nkeeline/KeeCap-Open-Motion-Capture-Suit/Build Procedures/IMG_2735.JPG

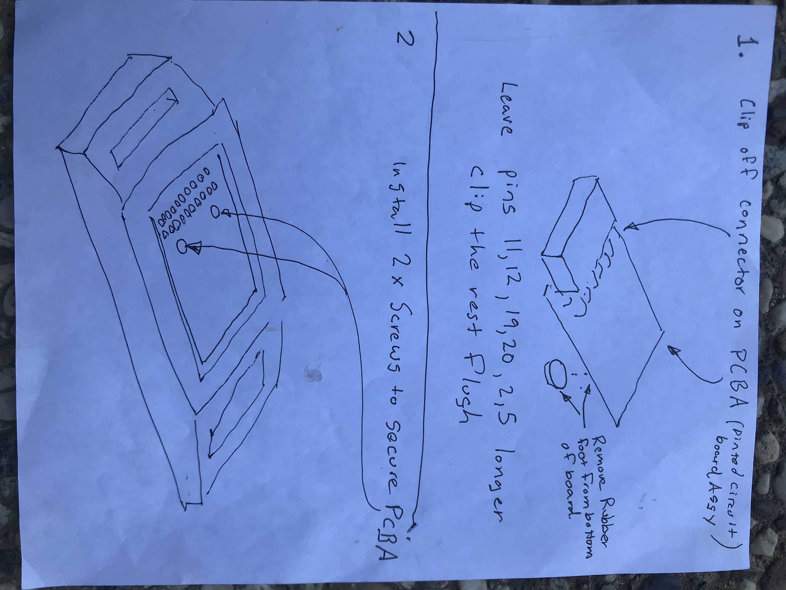
Build Procedures/IMG_2735.JPG
