nkeeline/KeeCap-Open-Motion-Capture-Suit/Build Procedures/IMG_2736.JPG

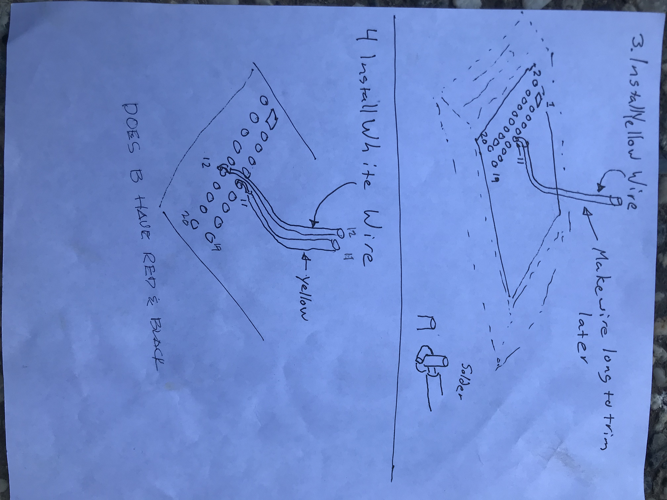
Build Procedures/IMG_2736.JPG
