nkeeline/KeeCap-Open-Motion-Capture-Suit/Build Procedures/IMG_2737.JPG

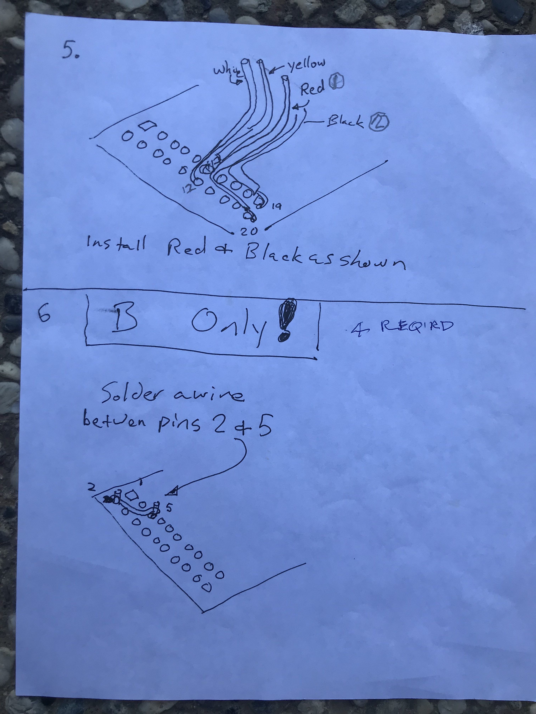
Build Procedures/IMG_2737.JPG
