nkeeline/KeeCap-Open-Motion-Capture-Suit/Build Procedures/IMG_2738.JPG

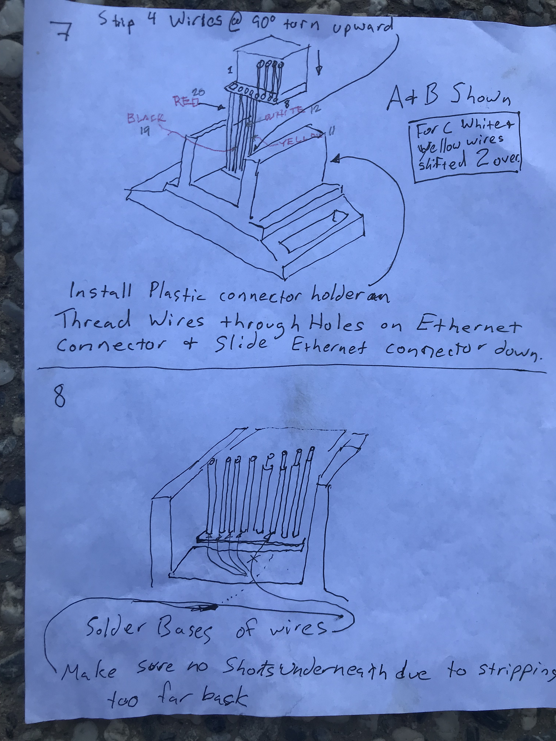
Build Procedures/IMG_2738.JPG
