nkeeline/KeeCap-Open-Motion-Capture-Suit/Build Procedures/IMG_2740.JPG

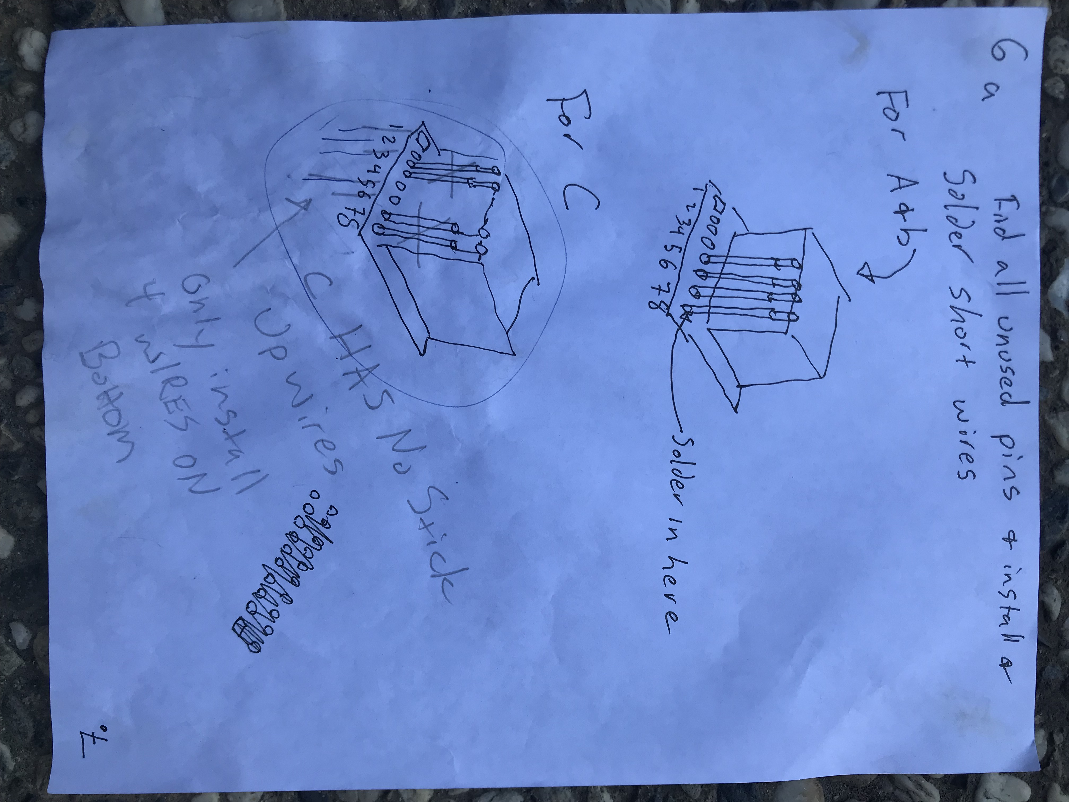
Build Procedures/IMG_2740.JPG
