nkeeline/KeeCap-Open-Motion-Capture-Suit/Build Procedures/Sensor Build 1.jpg

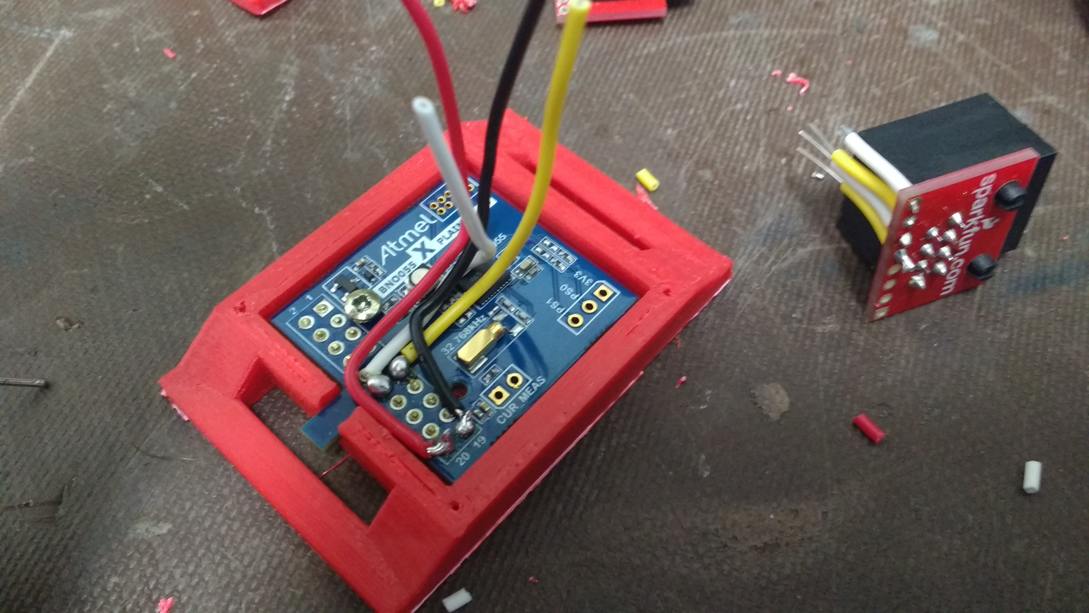
Build Procedures/Sensor Build 1.jpg
