nkeeline/KeeCap-Open-Motion-Capture-Suit/Build Procedures/Sensor Build 3.jpg

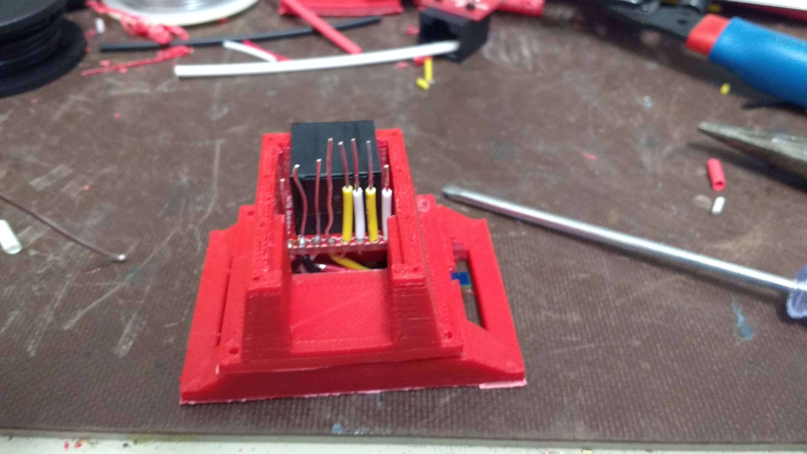
Build Procedures/Sensor Build 3.jpg
