nkeeline/KeeCap-Open-Motion-Capture-Suit/Build Procedures/Waist Build Procedure Pg3.jpg

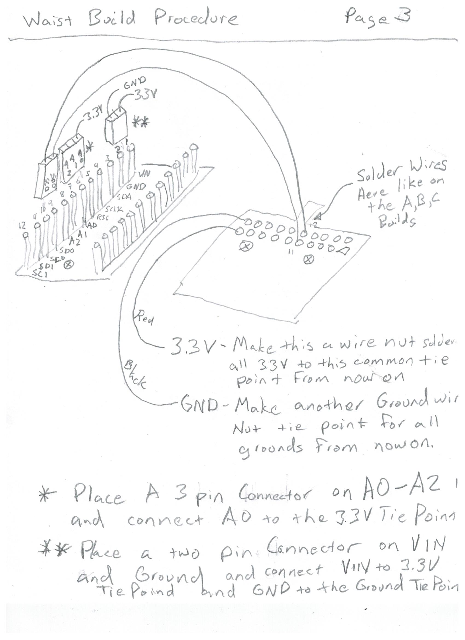
Build Procedures/Waist Build Procedure Pg3.jpg
