nkeeline/KeeCap-Open-Motion-Capture-Suit/Build Procedures/Waist Build Procedure Pg4.jpg

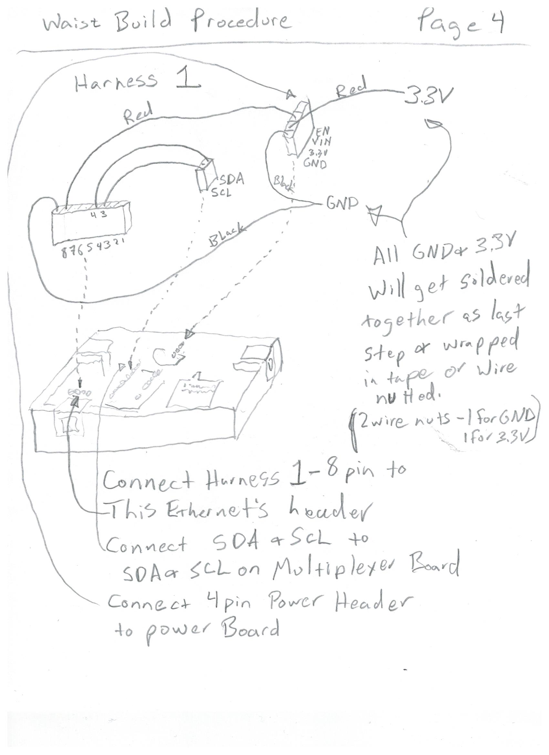
Build Procedures/Waist Build Procedure Pg4.jpg
